pdaxrom/p601zero/segled.v

module segled(
    input  [3:0] nibble,
    output reg [6:0]segs
);

	always @*
	case (nibble)
	4'b0000 :      	// Hexadecimal 0
		segs <= 7'b0111111;
	4'b0001 :    	// Hexadecimal 1
		segs <= 7'b0000110;
	4'b0010 :  		// Hexadecimal 2
		segs <= 7'b1011011; 
	4'b0011 : 		// Hexadecimal 3
		segs <= 7'b1001111;
	4'b0100 :		// Hexadecimal 4
		segs <= 7'b1100110;
	4'b0101 :		// Hexadecimal 5
		segs <= 7'b1101101;  
	4'b0110 :		// Hexadecimal 6
		segs <= 7'b1111101;
	4'b0111 :		// Hexadecimal 7
		segs <= 7'b0000111;
	4'b1000 :     	// Hexadecimal 8
		segs <= 7'b1111111;
	4'b1001 :    	// Hexadecimal 9
		segs <= 7'b1101111;
	4'b1010 :  		// Hexadecimal A
		segs <= 7'b1110111; 
	4'b1011 : 		// Hexadecimal B
		segs <= 7'b1111100;
	4'b1100 :		// Hexadecimal C
		segs <= 7'b0111001;
	4'b1101 :		// Hexadecimal D
		segs <= 7'b1011110;
	4'b1110 :		// Hexadecimal E
		segs <= 7'b1111001;
	4'b1111 :		// Hexadecimal F
		segs <= 7'b1110001;
	endcase
 
endmodule
